Final-Resolution/ChronoVolt/1.Hardware/ChronoVolt_Control_Rev0.3/datasheets/8-MD-06INKM模块/code/代码示例工程/test/source/n76e003/gpio.h

/**
 * @file gpio.h
 * @author mangolu (mangolu81@gmail.com)
 * @brief N76E003 GPIO设置定义
 * @version 1.0.0
 * @date 2019-04-21
 *
 * @copyright Copyright (c) 2019 mangolu All righits reserved
 *
 */
/********************************************************************************************************************************************************************************************************/
/************************* GPIO相关寄存器 *************************/

/************************************************** 1、输入输出数据控制相关寄存器 ***************************************************************************/

/************************* P0 – 端口 0 (可位寻址) *************************/
// -------------------------------------------------------------------------
// |   7    |   6    |   5    |   4    |   3    |   2    |   1    |   0    |
// |--------|--------|--------|--------|--------|--------|--------|--------|
// |  P0.7  |  P0.6  |  P0.5  |  P0.4  |  P0.3  |  P0.2  |  P0.1  |  P0.0  |
// |--------|--------|--------|--------|--------|--------|--------|--------|
// |  R/W   |  R/W   |  R/W   |  R/W   |  R/W   |  R/W   |  R/W   |  R/W   |
// -------------------------------------------------------------------------
// 地址：80H    复位值：1111 1111b
// 
// -------------------------------------------------------------------------
//   Bit  |   Name    |  Description
// -------|-----------|-----------------------------------------------------
//   7:0  |  P0[7:0]  |  端口 0
//        |           |  端口 0 是 8-bit 通用 I/O 端口
// -------------------------------------------------------------------------

/************************* P1 – 端口 1 (可位寻址) *************************/
// -------------------------------------------------------------------------
// |   7    |   6    |   5    |   4    |   3    |   2    |   1    |   0    |
// |--------|--------|--------|--------|--------|--------|--------|--------|
// |  P1.7  |  P1.6  |  P1.5  |  P1.4  |  P1.3  |  P1.2  |  P1.1  |  P1.0  |
// |--------|--------|--------|--------|--------|--------|--------|--------|
// |  R/W   |  R/W   |  R/W   |  R/W   |  R/W   |  R/W   |  R/W   |  R/W   |
// -------------------------------------------------------------------------
// 地址：90H    复位值：1111 1111b
// 
// -------------------------------------------------------------------------
//   Bit  |   Name    |  Description
// -------|-----------|-----------------------------------------------------
//   7:0  |  P1[7:0]  |  端口 1
//        |           |  端口 1 是 8-bit 通用 I/O 端口
// -------------------------------------------------------------------------

/************************* P2 – 端口 2 (可位寻址) *************************/
// -------------------------------------------------------------------------
// |   7    |   6    |   5    |   4    |   3    |   2    |   1    |   0    |
// |--------|--------|--------|--------|--------|--------|--------|--------|
// |   0    |   0    |   0    |   0    |   0    |   0    |   0    |  P2.0  |
// |--------|--------|--------|--------|--------|--------|--------|--------|
// |   R    |   R    |   R    |   R    |   R    |   R    |   R    |   R    |
// -------------------------------------------------------------------------
// 地址：A0H    复位值：0000 000Xb
// 
// -------------------------------------------------------------------------
//   Bit  |   Name    |  Description
// -------|-----------|-----------------------------------------------------
//   7:1  |    0      |  保留位
//        |           |  读取始终为0
// -------|-----------|-----------------------------------------------------
//    0   |   P2.0    |  端口 2 第 0 位
//        |           |  当RPD (CONFIG0.2)=0，P2.0为输入高阻管脚。不配置RPD， 
//        |           |  P2.0读取始终为0 
// -------------------------------------------------------------------------

/************************* P3 – 端口 3 (可位寻址) *************************/
// -------------------------------------------------------------------------
// |   7    |   6    |   5    |   4    |   3    |   2    |   1    |   0    |
// |--------|--------|--------|--------|--------|--------|--------|--------|
// |   0    |   0    |   0    |   0    |   0    |   0    |   0    |  P3.0  |
// |--------|--------|--------|--------|--------|--------|--------|--------|
// |   R    |   R    |   R    |   R    |   R    |   R    |   R    |  R/W   |
// -------------------------------------------------------------------------
// 地址：B0H    复位值：0000 0001b
// 
// -------------------------------------------------------------------------
//   Bit  |   Name    |  Description
// -------|-----------|-----------------------------------------------------
//   7:1  |    0      |  保留位
//        |           |  读取始终为0
// -------|-----------|-----------------------------------------------------
//    0   |   P3.0    |  端口 3 第 0 位
//        |           |  当采用内部振荡器作为系统时钟时，P3.0可用作普通管脚使用。
//        |           |  当采用外部晶振输入方式，P3.0脚用作OSCIN，此时对P3.0写
//        |           |  入数值无效，且P3.0读取值为0
// -------------------------------------------------------------------------

/************************************************** 2、输出模式控制寄存器 ***************************************************************************/

/************************* P0M1 – 端口 0模式选择1 *************************/
// -----------------------------------------------------------------------------------------
// |    7     |    6     |    5     |    4     |    3     |    2     |    1     |    0     |
// |----------|----------|----------|----------|----------|----------|----------|----------|
// |  P0M1.7  |  P0M1.6  |  P0M1.5  |  P0M1.4  |  P0M1.3  |  P0M1.2  |  P0M1.1  |  P0M1.0  |
// |----------|----------|----------|----------|----------|----------|----------|----------|
// |   R/W    |   R/W    |   R/W    |   R/W    |   R/W    |   R/W    |   R/W    |   R/W    |
// -----------------------------------------------------------------------------------------
// 地址：B1H, 页: 0    复位值：1111 1111b
// 
// ---------------------------------------------------------------------------
//   Bit  |   Name      |  Description
// -------|-------------|-----------------------------------------------------
//   7:0  |  P0M1[7:0]  |  端口 0 模式选择1
// ---------------------------------------------------------------------------
//  P0M1 和 P0M2 结合用于决定P0每个引脚的I/O模式

/************************* P0M2 – 端口 0 模式选择 2 *************************/
// -----------------------------------------------------------------------------------------
// |    7     |    6     |    5     |    4     |    3     |    2     |    1     |    0     |
// |----------|----------|----------|----------|----------|----------|----------|----------|
// |  P0M2.7  |  P0M2.7  |  P0M2.7  |  P0M2.7  |  P0M2.7  |  P0M2.7  |  P0M2.7  |  P0M2.7  |
// |----------|----------|----------|----------|----------|----------|----------|----------|
// |   R/W    |   R/W    |   R/W    |   R/W    |   R/W    |   R/W    |   R/W    |   R/W    |
// -----------------------------------------------------------------------------------------
// 地址：B2H, 页: 0    复位值：0000 0000b
// 
// ---------------------------------------------------------------------------
//   Bit  |   Name      |  Description
// -------|-------------|-----------------------------------------------------
//   7:0  |  P0M2[7:0]  |  端口 0 模式选择 2
// ---------------------------------------------------------------------------
// P0M1 和 P0M2 结合用于决定P0每个引脚的I/O模式

/************************* P1M1 – 端口 1 模式选择 1 *************************/
// -----------------------------------------------------------------------------------------
// |    7     |    6     |    5     |    4     |    3     |    2     |    1     |    0     |
// |----------|----------|----------|----------|----------|----------|----------|----------|
// |  P1M1.7  |  P1M1.6  |  P1M1.5  |  P1M1.4  |  P1M1.3  |  P1M1.2  |  P1M1.1  |  P1M1.0  |
// |----------|----------|----------|----------|----------|----------|----------|----------|
// |   R/W    |   R/W    |   R/W    |   R/W    |   R/W    |   R/W    |   R/W    |   R/W    |
// -----------------------------------------------------------------------------------------
// 地址：B3H, 页: 0    复位值：1111 1111b
// 
// ---------------------------------------------------------------------------
//   Bit  |   Name      |  Description
// -------|-------------|-----------------------------------------------------
//   7:0  |  P1M1[7:0]  |  端口 1 模式选择 1
// ---------------------------------------------------------------------------
// P1M1 和 P1M2 结合用于决定P1每个引脚的I/O模式

/************************* P1M2 – 端口 1 模式选择2 *************************/
// -----------------------------------------------------------------------------------------
// |    7     |    6     |    5     |    4     |    3     |    2     |    1     |    0     |
// |----------|----------|----------|----------|----------|----------|----------|----------|
// |  P1M2.7  |  P1M2.6  |  P1M2.5  |  P1M2.4  |  P1M2.3  |  P1M2.2  |  P1M2.1  |  P1M2.0  |
// |----------|----------|----------|----------|----------|----------|----------|----------|
// |   R/W    |   R/W    |   R/W    |   R/W    |   R/W    |   R/W    |   R/W    |   R/W    |
// -----------------------------------------------------------------------------------------
// 地址：B4H, 页: 0    复位值：0000 0000b
// 
// ---------------------------------------------------------------------------
//   Bit  |   Name      |  Description
// -------|-------------|-----------------------------------------------------
//   7:0  |  P1M2[7:0]  |  端口 1 模式选择2
// ---------------------------------------------------------------------------
// P1M1 和 P1M2 结合用于决定P1每个引脚的I/O模式

/************************* P2S – P20 设置及定时器0/1输出使能 *************************/
// ---------------------------------------------------------------------------
// |   7     |   6    |   5    |   4    |   3    |   2    |   1    |   0     |
// |---------|--------|--------|--------|--------|--------|--------|---------|
// |  P20UP  |   -    |   -    |   -    |  T1OE  |  T0OE  |   -    |  P2S.0  |
// |---------|--------|--------|--------|--------|--------|--------|---------|
// |  R/W    |   -    |   -    |   -    |  R/W   |  R/W   |   -    |  R/W    |
// ---------------------------------------------------------------------------
// 地址：B5H    复位值：0000 0000b
// 
// -------------------------------------------------------------------------------------
//   Bit  |   Name    |  Description
// -------|-----------|-----------------------------------------------------------------
//    7   |   P20UP   |  P2.0 上拉使能位
//        |           |  0 = P2.0 禁止上拉
//        |           |  1 = P2.0 使能上拉
//        |           |  仅当RPD (CONFIG0.2)为0时该位有效。如果作为RST#引脚，上拉总是被使能
// -------|-----------|-----------------------------------------------------------------
//    3   |   T1OE    |  定时器 1 输出使能位
//        |           |  0 = 禁止定时器 1 输出
//        |           |  1 = 使能定时器 1 输出从T1引脚
//        |           |  注意：仅当运行在定时器模式时，定时器1输出才会被使能
// -------|-----------|-----------------------------------------------------------------
//    2   |   T0OE    |  定时器 0 输出使能位
//        |           |  0 = 禁止定时器 0  输出
//        |           |  1 = 使能定时器 0  输出从T0引脚
//        |           |  注意：仅当运行在定时器模式时，定时器0输出才会被使能
// -------|-----------|-----------------------------------------------------------------
//    0   |   P2S.0   |  P2.0 施密特触发输入选择
//        |           |  0 = P2.0 TTL电平输入
//        |           |  1 = P2.0 施密特触发输入
// -------------------------------------------------------------------------------------

/************************* P3M1 – 端口 3 模式选择 1 *************************/
// ------------------------------------------------------------------------------
// |   7    |   6    |   5    |   4    |   3    |   2    |   1    |   0         |
// |--------|--------|--------|--------|--------|--------|--------|-------------|
// |   -    |   -    |   -    |   -    |   -    |   -    |   -    |  P3M1.0[3]  |
// |--------|--------|--------|--------|--------|--------|--------|-------------|
// |   -    |   -    |   -    |   -    |   -    |   -    |   -    |    R/W      |
// ------------------------------------------------------------------------------
// 地址：ACH, 页: 0    复位值：0000 0001b
// 
// -------------------------------------------------------------------------
//   Bit  |   Name    |  Description
// -------|-----------|-----------------------------------------------------
//    0   |  P3M1.0   |  端口 3 模式选择 1
// -------------------------------------------------------------------------
// [3] P3M1 和 P3M2结合用于决定P3每个引脚的I/O模式

/************************* P3M2 – 端口3 模式选择 2 *************************/
// ------------------------------------------------------------------------------
// |   7    |   6    |   5    |   4    |   3    |   2    |   1    |     0       |
// |--------|--------|--------|--------|--------|--------|--------|-------------|
// |   -    |   -    |   -    |   -    |   -    |   -    |   -    |  P3M2.0[3]  |
// |--------|--------|--------|--------|--------|--------|--------|-------------|
// |   -    |   -    |   -    |   -    |   -    |   -    |   -    |    R/W      |
// ------------------------------------------------------------------------------
// 地址：ADH, 页: 0    复位值：0000 0000b
// 
// -------------------------------------------------------------------------
//   Bit  |   Name    |  Description
// -------|-----------|-----------------------------------------------------
//    0   |  P3M2.0   |  端口3 模式选择 2
// -------------------------------------------------------------------------
// [3] P3M1 和 P3M2结合用于决定P3每个引脚的I/O模式

/************************************************** 3、输入类型寄存器 ***************************************************************************/

/************************* P0S – 端口 0 施密特触发输入 *************************/
// ---------------------------------------------------------------------------------
// |   7     |   6     |   5     |   4     |   3     |   2     |   1     |   0     |
// |---------|---------|---------|---------|---------|---------|---------|---------|
// |  P0S.7  |  P0S.6  |  P0S.5  |  P0S.4  |  P0S.3  |  P0S.2  |  P0S.1  |  P0S.0  |
// |---------|---------|---------|---------|---------|---------|---------|---------|
// |  R/W    |  R/W    |  R/W    |  R/W    |  R/W    |  R/W    |  R/W    |  R/W    |
// ---------------------------------------------------------------------------------
// 地址：B1H, 页: 1    复位值：0000 0000b
// 
// -------------------------------------------------------------------------
//   Bit  |   Name    |  Description
// -------|-----------|-----------------------------------------------------
//   7:0  |   P0S.n   |  P0.n 施密特触发输入使能位
//        |           |  0 = P0.n TTL 电平输入
//        |           |  1 = P0.n 施密特触发输入
// -------------------------------------------------------------------------

/************************* P1S – 端口 1施密特触发输入 *************************/
// ---------------------------------------------------------------------------------
// |   7     |   6     |   5     |   4     |   3     |   2     |   1     |   0     |
// |---------|---------|---------|---------|---------|---------|---------|---------|
// |  P1S.7  |  P1S.6  |  P1S.5  |  P1S.4  |  P1S.3  |  P1S.2  |  P1S.1  |  P1S.0  |
// |---------|---------|---------|---------|---------|---------|---------|---------|
// |  R/W    |  R/W    |  R/W    |  R/W    |  R/W    |  R/W    |  R/W    |  R/W    |
// ---------------------------------------------------------------------------------
// 地址：B3H, 页: 1    复位值：0000 0000b
// 
// -------------------------------------------------------------------------
//   Bit  |   Name    |  Description
// -------|-----------|-----------------------------------------------------
//   7:0  |   P1S.n   |  P1.n 施密特触发输入选择
//        |           |  0 = P1.n TTL电平输入
//        |           |  1 = P1.n 施密特触发输入
// -------------------------------------------------------------------------

/************************* P2S – P20 设置及定时器0/1输出使能 *************************/
// ---------------------------------------------------------------------------
// |   7     |   6    |   5    |   4    |   3    |   2    |   1    |   0     |
// |---------|--------|--------|--------|--------|--------|--------|---------|
// |  P20UP  |   -    |   -    |   -    |  T1OE  |  T0OE  |   -    |  P2S.0  |
// |---------|--------|--------|--------|--------|--------|--------|---------|
// |  R/W    |   -    |   -    |   -    |  R/W   |  R/W   |   -    |  R/W    |
// ---------------------------------------------------------------------------
// 地址：B5H    复位值：0000 0000b
// 
// -------------------------------------------------------------------------------------
//   Bit  |   Name    |  Description
// -------|-----------|-----------------------------------------------------------------
//    7   |   P20UP   |  P2.0 上拉使能位
//        |           |  0 = P2.0 禁止上拉
//        |           |  1 = P2.0 使能上拉
//        |           |  仅当RPD (CONFIG0.2)为0时该位有效。如果作为RST#引脚，上拉总是被使能
// -------|-----------|-----------------------------------------------------------------
//    3   |   T1OE    |  定时器 1 输出使能位
//        |           |  0 = 禁止定时器 1 输出
//        |           |  1 = 使能定时器 1 输出从T1引脚
//        |           |  注意：仅当运行在定时器模式时，定时器1输出才会被使能
// -------|-----------|-----------------------------------------------------------------
//    2   |   T0OE    |  定时器 0 输出使能位
//        |           |  0 = 禁止定时器 0  输出
//        |           |  1 = 使能定时器 0  输出从T0引脚
//        |           |  注意：仅当运行在定时器模式时，定时器0输出才会被使能
// -------|-----------|-----------------------------------------------------------------
//    0   |   P2S.0   |  P2.0 施密特触发输入选择
//        |           |  0 = P2.0 TTL电平输入
//        |           |  1 = P2.0 施密特触发输入
// -------------------------------------------------------------------------------------

/************************* P3S – 端口 3施密特触发输入 *************************/
// --------------------------------------------------------------------------
// |   7    |   6    |   5    |   4    |   3    |   2    |   1    |   0     |
// |--------|--------|--------|--------|--------|--------|--------|---------|
// |   -    |   -    |   -    |   -    |   -    |   -    |   -    |  P3S.0  |
// |--------|--------|--------|--------|--------|--------|--------|---------|
// |   -    |   -    |   -    |   -    |   -    |   -    |   -    |  R/W    |
// --------------------------------------------------------------------------
// 地址：ACH, 页: 1    复位值：0000 0000b
// 
// -------------------------------------------------------------------------
//   Bit  |   Name    |  Description
// -------|-----------|-----------------------------------------------------
//    0   |  P3S.0    |  P3.0 施密特触发输入选择
//        |           |  0 = P3.0 TTL电平输入
//        |           |  1 = P3.0 施密特触发输入
// -------------------------------------------------------------------------

/************************************************** 4、输出斜率控制寄存器 ***************************************************************************/

/************************* P0SR – 端口 0 斜率控制 *************************/
// -----------------------------------------------------------------------------------------
// |    7     |    6     |    5     |    4     |    3     |    2     |    1     |    0     |
// |----------|----------|----------|----------|----------|----------|----------|----------|
// |  P0SR.7  |  P0SR.6  |  P0SR.5  |  P0SR.4  |  P0SR.3  |  P0SR.2  |  P0SR.1  |  P0SR.0  |
// |----------|----------|----------|----------|----------|----------|----------|----------|
// |   R/W    |   R/W    |   R/W    |   R/W    |   R/W    |   R/W    |   R/W    |   R/W    |
// -----------------------------------------------------------------------------------------
// 地址：B2H, 页: 1    复位值：0000 0000b
// 
// -------------------------------------------------------------------------
//   Bit  |   Name    |  Description
// -------|-----------|-----------------------------------------------------
//   7:0  |  P0SR.n   |  P0.n 斜率控制
//        |           |  0 = P0.n 普通输出
//        |           |  1 = P0.n 高速输出
// -------------------------------------------------------------------------

/************************* P1SR – 端口 1 斜率控制 *************************/
// -----------------------------------------------------------------------------------------
// |    7     |    6     |    5     |    4     |    3     |    2     |    1     |    0     |
// |----------|----------|----------|----------|----------|----------|----------|----------|
// |  P1SR.7  |  P1SR.6  |  P1SR.5  |  P1SR.4  |  P1SR.3  |  P1SR.2  |  P1SR.1  |  P1SR.0  |
// |----------|----------|----------|----------|----------|----------|----------|----------|
// |   R/W    |   R/W    |   R/W    |   R/W    |   R/W    |   R/W    |   R/W    |   R/W    |
// -----------------------------------------------------------------------------------------
// 地址：B4H, 页: 1    复位值：0000 0000b
// 
// -------------------------------------------------------------------------
//   Bit  |   Name    |  Description
// -------|-----------|-----------------------------------------------------
//   7:0  |  P1SR.n   |  P1.n 斜率控制
//        |           |  0 = P1.n 普通输出
//        |           |  1 = P1.n 高速输出
// -------------------------------------------------------------------------

/************************* P3SR – 端口 3 斜率控制 *************************/
// ---------------------------------------------------------------------------
// |   7    |   6    |   5    |   4    |   3    |   2    |   1    |    0     |
// |--------|--------|--------|--------|--------|--------|--------|----------|
// |   -    |   -    |   -    |   -    |   -    |   -    |   -    |  P3SR.0  |
// |--------|--------|--------|--------|--------|--------|--------|----------|
// |   -    |   -    |   -    |   -    |   -    |   -    |   -    |   R/W    |
// ---------------------------------------------------------------------------
// 地址：ADH, 页: 1    复位值：0000 0000b
// 
// -------------------------------------------------------------------------
//   Bit  |   Name    |  Description
// -------|-----------|-----------------------------------------------------
//    0   |  P3SR.0   |  P3.n 斜率控制
//        |           |  0 = P3.0 普通输出
//        |           |  1 = P3.0 高速输出
// -------------------------------------------------------------------------

/********************************************************************************************************************************************************************************************************/
#ifndef _GPIO_H_
#define _GPIO_H_

/** 所需头文件开始>>> */

#include "N76E003.h"
#include "../common/common.h"

/** 所需头文件结束<<< */

/** 需要自行定义部分开始>>> */

extern bit BIT_TMP;	/** 比特位存储临时变量，定义于common.c文件中 */

/** 需要自行定义部分结束<<< */

/********************************************************************************************************************************************************************************************************/
/************************* 设置端口为准双向模式(Quasi Mode)（标准8051端口结构） *************************/
#define SET_P00_Quasi_Mode		P0M1&=~SET_BIT0;P0M2&=~SET_BIT0		/** 设置P0^0为准双向模式 */
#define SET_P01_Quasi_Mode		P0M1&=~SET_BIT1;P0M2&=~SET_BIT1		/** 设置P0^1为准双向模式 */
#define SET_P02_Quasi_Mode		P0M1&=~SET_BIT2;P0M2&=~SET_BIT2		/** 设置P0^2为准双向模式 */
#define SET_P03_Quasi_Mode		P0M1&=~SET_BIT3;P0M2&=~SET_BIT3		/** 设置P0^3为准双向模式 */
#define SET_P04_Quasi_Mode		P0M1&=~SET_BIT4;P0M2&=~SET_BIT4		/** 设置P0^4为准双向模式 */
#define SET_P05_Quasi_Mode		P0M1&=~SET_BIT5;P0M2&=~SET_BIT5		/** 设置P0^5为准双向模式 */
#define SET_P06_Quasi_Mode		P0M1&=~SET_BIT6;P0M2&=~SET_BIT6		/** 设置P0^6为准双向模式 */
#define SET_P07_Quasi_Mode		P0M1&=~SET_BIT7;P0M2&=~SET_BIT7		/** 设置P0^7为准双向模式 */
#define SET_P10_Quasi_Mode		P1M1&=~SET_BIT0;P1M2&=~SET_BIT0		/** 设置P1^0为准双向模式 */
#define SET_P11_Quasi_Mode		P1M1&=~SET_BIT1;P1M2&=~SET_BIT1		/** 设置P1^1为准双向模式 */
#define SET_P12_Quasi_Mode		P1M1&=~SET_BIT2;P1M2&=~SET_BIT2		/** 设置P1^2为准双向模式 */
#define SET_P13_Quasi_Mode		P1M1&=~SET_BIT3;P1M2&=~SET_BIT3		/** 设置P1^3为准双向模式 */
#define SET_P14_Quasi_Mode		P1M1&=~SET_BIT4;P1M2&=~SET_BIT4		/** 设置P1^4为准双向模式 */
#define SET_P15_Quasi_Mode		P1M1&=~SET_BIT5;P1M2&=~SET_BIT5		/** 设置P1^5为准双向模式 */
#define SET_P16_Quasi_Mode		P1M1&=~SET_BIT6;P1M2&=~SET_BIT6		/** 设置P1^6为准双向模式 */
#define SET_P17_Quasi_Mode		P1M1&=~SET_BIT7;P1M2&=~SET_BIT7		/** 设置P1^7为准双向模式 */
#define SET_P30_Quasi_Mode		P3M1&=~SET_BIT0;P3M2&=~SET_BIT0		/** 设置P3^0为准双向模式 */
#define SET_P0_Quasi_Mode		P0M1=0x00;P0M2=0x00					/** 设置P0端口为准双向模式 */
#define SET_P1_Quasi_Mode		P1M1=0x00;P1M2=0x00					/** 设置P1端口为准双向模式 */

/********************************************************************************************************************************************************************************************************/

/********************************************************************************************************************************************************************************************************/
/************************* 设置端口为推挽输出模式(Push Pull Mode) *************************/
#define SET_P00_PushPull_Mode		P0M1&=~SET_BIT0;P0M2|=SET_BIT0		/** 设置P0^0为推挽输出模式 */
#define SET_P01_PushPull_Mode		P0M1&=~SET_BIT1;P0M2|=SET_BIT1		/** 设置P0^1为推挽输出模式 */
#define SET_P02_PushPull_Mode		P0M1&=~SET_BIT2;P0M2|=SET_BIT2		/** 设置P0^2为推挽输出模式 */
#define SET_P03_PushPull_Mode		P0M1&=~SET_BIT3;P0M2|=SET_BIT3		/** 设置P0^3为推挽输出模式 */
#define SET_P04_PushPull_Mode		P0M1&=~SET_BIT4;P0M2|=SET_BIT4		/** 设置P0^4为推挽输出模式 */
#define SET_P05_PushPull_Mode		P0M1&=~SET_BIT5;P0M2|=SET_BIT5		/** 设置P0^5为推挽输出模式 */
#define SET_P06_PushPull_Mode		P0M1&=~SET_BIT6;P0M2|=SET_BIT6		/** 设置P0^6为推挽输出模式 */
#define SET_P07_PushPull_Mode		P0M1&=~SET_BIT7;P0M2|=SET_BIT7		/** 设置P0^7为推挽输出模式 */
#define SET_P10_PushPull_Mode		P1M1&=~SET_BIT0;P1M2|=SET_BIT0		/** 设置P1^0为推挽输出模式 */
#define SET_P11_PushPull_Mode		P1M1&=~SET_BIT1;P1M2|=SET_BIT1		/** 设置P1^1为推挽输出模式 */
#define SET_P12_PushPull_Mode		P1M1&=~SET_BIT2;P1M2|=SET_BIT2		/** 设置P1^2为推挽输出模式 */
#define SET_P13_PushPull_Mode		P1M1&=~SET_BIT3;P1M2|=SET_BIT3		/** 设置P1^3为推挽输出模式 */
#define SET_P14_PushPull_Mode		P1M1&=~SET_BIT4;P1M2|=SET_BIT4		/** 设置P1^4为推挽输出模式 */
#define SET_P15_PushPull_Mode		P1M1&=~SET_BIT5;P1M2|=SET_BIT5		/** 设置P1^5为推挽输出模式 */
#define SET_P16_PushPull_Mode		P1M1&=~SET_BIT6;P1M2|=SET_BIT6		/** 设置P1^6为推挽输出模式 */
#define SET_P17_PushPull_Mode		P1M1&=~SET_BIT7;P1M2|=SET_BIT7		/** 设置P1^7为推挽输出模式 */
#define SET_P30_PushPull_Mode		P3M1&=~SET_BIT0;P3M2|=SET_BIT0		/** 设置P3^0为推挽输出模式 */
#define SET_P0_PushPull_Mode		P0M1=0x00;P0M2=0xFF					/** 设置P0端口为推挽输出模式 */
#define SET_P1_PushPull_Mode		P1M1=0x00;P1M2=0xFF					/** 设置P1端口为推挽输出模式 */

/********************************************************************************************************************************************************************************************************/

/********************************************************************************************************************************************************************************************************/
/************************* 设置端口为输入模式(高阻)(Input Only Mode) *************************/
#define SET_P00_Input_Mode		P0M1|=SET_BIT0;P0M2&=~SET_BIT0		/** 设置P0^0为输入模式 */
#define SET_P01_Input_Mode		P0M1|=SET_BIT1;P0M2&=~SET_BIT1		/** 设置P0^1为输入模式 */
#define SET_P02_Input_Mode		P0M1|=SET_BIT2;P0M2&=~SET_BIT2		/** 设置P0^2为输入模式 */
#define SET_P03_Input_Mode		P0M1|=SET_BIT3;P0M2&=~SET_BIT3		/** 设置P0^3为输入模式 */
#define SET_P04_Input_Mode		P0M1|=SET_BIT4;P0M2&=~SET_BIT4		/** 设置P0^4为输入模式 */
#define SET_P05_Input_Mode		P0M1|=SET_BIT5;P0M2&=~SET_BIT5		/** 设置P0^5为输入模式 */
#define SET_P06_Input_Mode		P0M1|=SET_BIT6;P0M2&=~SET_BIT6		/** 设置P0^6为输入模式 */
#define SET_P07_Input_Mode		P0M1|=SET_BIT7;P0M2&=~SET_BIT7		/** 设置P0^7为输入模式 */
#define SET_P10_Input_Mode		P1M1|=SET_BIT0;P1M2&=~SET_BIT0		/** 设置P1^0为输入模式 */
#define SET_P11_Input_Mode		P1M1|=SET_BIT1;P1M2&=~SET_BIT1		/** 设置P1^1为输入模式 */
#define SET_P12_Input_Mode		P1M1|=SET_BIT2;P1M2&=~SET_BIT2		/** 设置P1^2为输入模式 */
#define SET_P13_Input_Mode		P1M1|=SET_BIT3;P1M2&=~SET_BIT3		/** 设置P1^3为输入模式 */
#define SET_P14_Input_Mode		P1M1|=SET_BIT4;P1M2&=~SET_BIT4		/** 设置P1^4为输入模式 */
#define SET_P15_Input_Mode		P1M1|=SET_BIT5;P1M2&=~SET_BIT5		/** 设置P1^5为输入模式 */
#define SET_P16_Input_Mode		P1M1|=SET_BIT6;P1M2&=~SET_BIT6		/** 设置P1^6为输入模式 */
#define SET_P17_Input_Mode		P1M1|=SET_BIT7;P1M2&=~SET_BIT7		/** 设置P1^7为输入模式 */
#define SET_P30_Input_Mode		P3M1|=SET_BIT0;P3M2&=~SET_BIT0		/** 设置P3^0为输入模式 */
#define SET_P0_Input_Mode		P0M1=0xFF;P0M2=0x00					/** 设置P0端口为输入模式 */
#define SET_P1_Input_Mode		P1M1=0xFF;P1M2=0x00					/** 设置P1端口为输入模式 */

/********************************************************************************************************************************************************************************************************/

/********************************************************************************************************************************************************************************************************/
/************************* 设置端口为开漏模式(Open Drain Mode) *************************/
#define SET_P00_OpenDrain_Mode		P0M1|=SET_BIT0;P0M2|=SET_BIT0		/** 设置P0^0为开漏模式 */
#define SET_P01_OpenDrain_Mode		P0M1|=SET_BIT1;P0M2|=SET_BIT1		/** 设置P0^1为开漏模式 */
#define SET_P02_OpenDrain_Mode		P0M1|=SET_BIT2;P0M2|=SET_BIT2		/** 设置P0^2为开漏模式 */
#define SET_P03_OpenDrain_Mode		P0M1|=SET_BIT3;P0M2|=SET_BIT3		/** 设置P0^3为开漏模式 */
#define SET_P04_OpenDrain_Mode		P0M1|=SET_BIT4;P0M2|=SET_BIT4		/** 设置P0^4为开漏模式 */
#define SET_P05_OpenDrain_Mode		P0M1|=SET_BIT5;P0M2|=SET_BIT5		/** 设置P0^5为开漏模式 */
#define SET_P06_OpenDrain_Mode		P0M1|=SET_BIT6;P0M2|=SET_BIT6		/** 设置P0^6为开漏模式 */
#define SET_P07_OpenDrain_Mode		P0M1|=SET_BIT7;P0M2|=SET_BIT7		/** 设置P0^7为开漏模式 */
#define SET_P10_OpenDrain_Mode		P1M1|=SET_BIT0;P1M2|=SET_BIT0		/** 设置P1^0为开漏模式 */
#define SET_P11_OpenDrain_Mode		P1M1|=SET_BIT1;P1M2|=SET_BIT1		/** 设置P1^1为开漏模式 */
#define SET_P12_OpenDrain_Mode		P1M1|=SET_BIT2;P1M2|=SET_BIT2		/** 设置P1^2为开漏模式 */
#define SET_P13_OpenDrain_Mode		P1M1|=SET_BIT3;P1M2|=SET_BIT3		/** 设置P1^3为开漏模式 */
#define SET_P14_OpenDrain_Mode		P1M1|=SET_BIT4;P1M2|=SET_BIT4		/** 设置P1^4为开漏模式 */
#define SET_P15_OpenDrain_Mode		P1M1|=SET_BIT5;P1M2|=SET_BIT5		/** 设置P1^5为开漏模式 */
#define SET_P16_OpenDrain_Mode		P1M1|=SET_BIT6;P1M2|=SET_BIT6		/** 设置P1^6为开漏模式 */
#define SET_P17_OpenDrain_Mode		P1M1|=SET_BIT7;P1M2|=SET_BIT7		/** 设置P1^7为开漏模式 */
#define SET_P30_OpenDrain_Mode		P3M1|=SET_BIT0;P3M2|=SET_BIT0		/** 设置P3^0为开漏模式 */
#define SET_P0_OpenDrain_Mode		P0M1=0xFF;P0M2=0xFF					/** 设置P0端口为开漏模式 */
#define SET_P1_OpenDrain_Mode		P1M1=0xFF;P1M2=0xFF					/** 设置P1端口为开漏模式 */

/********************************************************************************************************************************************************************************************************/

/********************************************************************************************************************************************************************************************************/
/************************* 设置P0端口输入类型(默认为TTL输入类型) *************************/
#define SET_P00_TTL_INPUT_TYPE			BIT_TMP=EA;EA=0;TA=0xAA;TA=0x55;SFRS=0x01;P0S&=~SET_BIT0;TA=0xAA;TA=0x55;SFRS=0x00;EA=BIT_TMP		/** 设置P0^0为TTL输入类型 */
#define SET_P01_TTL_INPUT_TYPE			BIT_TMP=EA;EA=0;TA=0xAA;TA=0x55;SFRS=0x01;P0S&=~SET_BIT1;TA=0xAA;TA=0x55;SFRS=0x00;EA=BIT_TMP		/** 设置P0^1为TTL输入类型 */
#define SET_P02_TTL_INPUT_TYPE			BIT_TMP=EA;EA=0;TA=0xAA;TA=0x55;SFRS=0x01;P0S&=~SET_BIT2;TA=0xAA;TA=0x55;SFRS=0x00;EA=BIT_TMP		/** 设置P0^2为TTL输入类型 */
#define SET_P03_TTL_INPUT_TYPE			BIT_TMP=EA;EA=0;TA=0xAA;TA=0x55;SFRS=0x01;P0S&=~SET_BIT3;TA=0xAA;TA=0x55;SFRS=0x00;EA=BIT_TMP		/** 设置P0^3为TTL输入类型 */
#define SET_P04_TTL_INPUT_TYPE			BIT_TMP=EA;EA=0;TA=0xAA;TA=0x55;SFRS=0x01;P0S&=~SET_BIT4;TA=0xAA;TA=0x55;SFRS=0x00;EA=BIT_TMP		/** 设置P0^4为TTL输入类型 */
#define SET_P05_TTL_INPUT_TYPE			BIT_TMP=EA;EA=0;TA=0xAA;TA=0x55;SFRS=0x01;P0S&=~SET_BIT5;TA=0xAA;TA=0x55;SFRS=0x00;EA=BIT_TMP		/** 设置P0^5为TTL输入类型 */
#define SET_P06_TTL_INPUT_TYPE			BIT_TMP=EA;EA=0;TA=0xAA;TA=0x55;SFRS=0x01;P0S&=~SET_BIT6;TA=0xAA;TA=0x55;SFRS=0x00;EA=BIT_TMP		/** 设置P0^6为TTL输入类型 */
#define SET_P07_TTL_INPUT_TYPE			BIT_TMP=EA;EA=0;TA=0xAA;TA=0x55;SFRS=0x01;P0S&=~SET_BIT7;TA=0xAA;TA=0x55;SFRS=0x00;EA=BIT_TMP		/** 设置P0^7为TTL输入类型 */

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

/********************************************************************************************************************************************************************************************************/

/********************************************************************************************************************************************************************************************************/
/************************* 设置P2端口输入类型(默认为TTL输入类型)(P2^0只能做为输入，不能做输出) *************************/
#define SET_P20_TTL_INPUT_TYPE			BIT_TMP=EA;EA=0;TA=0xAA;TA=0x55;SFRS=0x01;P2S&=~SET_BIT0;TA=0xAA;TA=0x55;SFRS=0x00;EA=BIT_TMP		/** 设置P2^0为TTL输入类型 */

/************************* 设置P2端口输入类型(默认为史密斯触发输入类型)(P2^0只能做为输入，不能做输出) *************************/
#define SET_P20_SCHMITT_INPUT_TYPE		BIT_TMP=EA;EA=0;TA=0xAA;TA=0x55;SFRS=0x01;P2S|=SET_BIT0;TA=0xAA;TA=0x55;SFRS=0x00;EA=BIT_TMP		/** 设置P2^0为史密斯触发输入类型 */

/********************************************************************************************************************************************************************************************************/

/********************************************************************************************************************************************************************************************************/

/************************* 设置P3端口输入类型(默认为TTL输入类型)(P2^0只能做为输入，不能做输出) *************************/
#define SET_P30_TTL_INPUT_TYPE			BIT_TMP=EA;EA=0;TA=0xAA;TA=0x55;SFRS=0x01;P3S&=~SET_BIT0;TA=0xAA;TA=0x55;SFRS=0x00;EA=BIT_TMP		/** 设置P3^0为TTL输入类型 */

/************************* 设置P3端口输入类型(默认为史密斯触发输入类型)(P2^0只能做为输入，不能做输出) *************************/
#define SET_P30_SCHMITT_INPUT_TYPE		BIT_TMP=EA;EA=0;TA=0xAA;TA=0x55;SFRS=0x01;P3S|=SET_BIT0;TA=0xAA;TA=0x55;SFRS=0x00;EA=BIT_TMP		/** 设置P3^0为史密斯触发输入类型 */

/********************************************************************************************************************************************************************************************************/

/********************************************************************************************************************************************************************************************************/

/************************* 设置P0端口输出斜率为普通输出(默认为普通输出) *************************/
#define SET_P00_OUTPUT_SLEW_RATE_NORMAL_SPEED		BIT_TMP=EA;EA=0;TA=0xAA;TA=0x55;SFRS=0x01;P0SR&=~SET_BIT0;TA=0xAA;TA=0x55;SFRS=0x00;EA=BIT_TMP	/** 设置端口P0^0输出斜率为普通输出 */
#define SET_P01_OUTPUT_SLEW_RATE_NORMAL_SPEED		BIT_TMP=EA;EA=0;TA=0xAA;TA=0x55;SFRS=0x01;P0SR&=~SET_BIT1;TA=0xAA;TA=0x55;SFRS=0x00;EA=BIT_TMP	/** 设置端口P0^1输出斜率为普通输出 */
#define SET_P02_OUTPUT_SLEW_RATE_NORMAL_SPEED		BIT_TMP=EA;EA=0;TA=0xAA;TA=0x55;SFRS=0x01;P0SR&=~SET_BIT2;TA=0xAA;TA=0x55;SFRS=0x00;EA=BIT_TMP	/** 设置端口P0^2输出斜率为普通输出 */
#define SET_P03_OUTPUT_SLEW_RATE_NORMAL_SPEED		BIT_TMP=EA;EA=0;TA=0xAA;TA=0x55;SFRS=0x01;P0SR&=~SET_BIT3;TA=0xAA;TA=0x55;SFRS=0x00;EA=BIT_TMP	/** 设置端口P0^3输出斜率为普通输出 */
#define SET_P04_OUTPUT_SLEW_RATE_NORMAL_SPEED		BIT_TMP=EA;EA=0;TA=0xAA;TA=0x55;SFRS=0x01;P0SR&=~SET_BIT4;TA=0xAA;TA=0x55;SFRS=0x00;EA=BIT_TMP	/** 设置端口P0^4输出斜率为普通输出 */
#define SET_P05_OUTPUT_SLEW_RATE_NORMAL_SPEED		BIT_TMP=EA;EA=0;TA=0xAA;TA=0x55;SFRS=0x01;P0SR&=~SET_BIT5;TA=0xAA;TA=0x55;SFRS=0x00;EA=BIT_TMP	/** 设置端口P0^5输出斜率为普通输出 */
#define SET_P06_OUTPUT_SLEW_RATE_NORMAL_SPEED		BIT_TMP=EA;EA=0;TA=0xAA;TA=0x55;SFRS=0x01;P0SR&=~SET_BIT6;TA=0xAA;TA=0x55;SFRS=0x00;EA=BIT_TMP	/** 设置端口P0^6输出斜率为普通输出 */
#define SET_P07_OUTPUT_SLEW_RATE_NORMAL_SPEED		BIT_TMP=EA;EA=0;TA=0xAA;TA=0x55;SFRS=0x01;P0SR&=~SET_BIT7;TA=0xAA;TA=0x55;SFRS=0x00;EA=BIT_TMP	/** 设置端口P0^7输出斜率为普通输出 */
#define SET_P0_OUTPUT_SLEW_RATE_NORMAL_SPEED		BIT_TMP=EA;EA=0;TA=0xAA;TA=0x55;SFRS=0x01;P0SR=0x00;TA=0xAA;TA=0x55;SFRS=0x00;EA=BIT_TMP		/** 设置端口P0输出斜率为普通输出 */

/************************* 设置P0端口输出斜率为高速输出(默认为普通输出) *************************/
#define SET_P00_OUTPUT_SLEW_RATE_HIGH_SPEED			BIT_TMP=EA;EA=0;TA=0xAA;TA=0x55;SFRS=0x01;P0SR|=SET_BIT0;TA=0xAA;TA=0x55;SFRS=0x00;EA=BIT_TMP	/** 设置端口P0^0输出斜率为高速输出 */
#define SET_P01_OUTPUT_SLEW_RATE_HIGH_SPEED			BIT_TMP=EA;EA=0;TA=0xAA;TA=0x55;SFRS=0x01;P0SR|=SET_BIT1;TA=0xAA;TA=0x55;SFRS=0x00;EA=BIT_TMP	/** 设置端口P0^1输出斜率为高速输出 */
#define SET_P02_OUTPUT_SLEW_RATE_HIGH_SPEED			BIT_TMP=EA;EA=0;TA=0xAA;TA=0x55;SFRS=0x01;P0SR|=SET_BIT2;TA=0xAA;TA=0x55;SFRS=0x00;EA=BIT_TMP	/** 设置端口P0^2输出斜率为高速输出 */
#define SET_P03_OUTPUT_SLEW_RATE_HIGH_SPEED			BIT_TMP=EA;EA=0;TA=0xAA;TA=0x55;SFRS=0x01;P0SR|=SET_BIT3;TA=0xAA;TA=0x55;SFRS=0x00;EA=BIT_TMP	/** 设置端口P0^3输出斜率为高速输出 */
#define SET_P04_OUTPUT_SLEW_RATE_HIGH_SPEED			BIT_TMP=EA;EA=0;TA=0xAA;TA=0x55;SFRS=0x01;P0SR|=SET_BIT4;TA=0xAA;TA=0x55;SFRS=0x00;EA=BIT_TMP	/** 设置端口P0^4输出斜率为高速输出 */
#define SET_P05_OUTPUT_SLEW_RATE_HIGH_SPEED			BIT_TMP=EA;EA=0;TA=0xAA;TA=0x55;SFRS=0x01;P0SR|=SET_BIT5;TA=0xAA;TA=0x55;SFRS=0x00;EA=BIT_TMP	/** 设置端口P0^5输出斜率为高速输出 */
#define SET_P06_OUTPUT_SLEW_RATE_HIGH_SPEED			BIT_TMP=EA;EA=0;TA=0xAA;TA=0x55;SFRS=0x01;P0SR|=SET_BIT6;TA=0xAA;TA=0x55;SFRS=0x00;EA=BIT_TMP	/** 设置端口P0^6输出斜率为高速输出 */
#define SET_P07_OUTPUT_SLEW_RATE_HIGH_SPEED			BIT_TMP=EA;EA=0;TA=0xAA;TA=0x55;SFRS=0x01;P0SR|=SET_BIT7;TA=0xAA;TA=0x55;SFRS=0x00;EA=BIT_TMP	/** 设置端口P0^7输出斜率为高速输出 */
#define SET_P0_OUTPUT_SLEW_RATE_HIGH_SPEED			BIT_TMP=EA;EA=0;TA=0xAA;TA=0x55;SFRS=0x01;P0SR=0xFF;TA=0xAA;TA=0x55;SFRS=0x00;EA=BIT_TMP		/** 设置端口P0输出斜率为高速输出 */

/********************************************************************************************************************************************************************************************************/

/********************************************************************************************************************************************************************************************************/
/************************* 设置P1端口输出斜率为普通输出(默认为普通输出) *************************/
#define SET_P10_OUTPUT_SLEW_RATE_NORMAL_SPEED		BIT_TMP=EA;EA=0;TA=0xAA;TA=0x55;SFRS=0x01;P1SR&=~SET_BIT0;TA=0xAA;TA=0x55;SFRS=0x00;EA=BIT_TMP	/** 设置端口P1^0输出斜率为普通输出 */
#define SET_P11_OUTPUT_SLEW_RATE_NORMAL_SPEED		BIT_TMP=EA;EA=0;TA=0xAA;TA=0x55;SFRS=0x01;P1SR&=~SET_BIT1;TA=0xAA;TA=0x55;SFRS=0x00;EA=BIT_TMP	/** 设置端口P1^1输出斜率为普通输出 */
#define SET_P12_OUTPUT_SLEW_RATE_NORMAL_SPEED		BIT_TMP=EA;EA=0;TA=0xAA;TA=0x55;SFRS=0x01;P1SR&=~SET_BIT2;TA=0xAA;TA=0x55;SFRS=0x00;EA=BIT_TMP	/** 设置端口P1^2输出斜率为普通输出 */
#define SET_P13_OUTPUT_SLEW_RATE_NORMAL_SPEED		BIT_TMP=EA;EA=0;TA=0xAA;TA=0x55;SFRS=0x01;P1SR&=~SET_BIT3;TA=0xAA;TA=0x55;SFRS=0x00;EA=BIT_TMP	/** 设置端口P1^3输出斜率为普通输出 */
#define SET_P14_OUTPUT_SLEW_RATE_NORMAL_SPEED		BIT_TMP=EA;EA=0;TA=0xAA;TA=0x55;SFRS=0x01;P1SR&=~SET_BIT4;TA=0xAA;TA=0x55;SFRS=0x00;EA=BIT_TMP	/** 设置端口P1^4输出斜率为普通输出 */
#define SET_P15_OUTPUT_SLEW_RATE_NORMAL_SPEED		BIT_TMP=EA;EA=0;TA=0xAA;TA=0x55;SFRS=0x01;P1SR&=~SET_BIT5;TA=0xAA;TA=0x55;SFRS=0x00;EA=BIT_TMP	/** 设置端口P1^5输出斜率为普通输出 */
#define SET_P16_OUTPUT_SLEW_RATE_NORMAL_SPEED		BIT_TMP=EA;EA=0;TA=0xAA;TA=0x55;SFRS=0x01;P1SR&=~SET_BIT6;TA=0xAA;TA=0x55;SFRS=0x00;EA=BIT_TMP	/** 设置端口P1^6输出斜率为普通输出 */
#define SET_P17_OUTPUT_SLEW_RATE_NORMAL_SPEED		BIT_TMP=EA;EA=0;TA=0xAA;TA=0x55;SFRS=0x01;P1SR&=~SET_BIT7;TA=0xAA;TA=0x55;SFRS=0x00;EA=BIT_TMP	/** 设置端口P1^7输出斜率为普通输出 */
#define SET_P1_OUTPUT_SLEW_RATE_NORMAL_SPEED		BIT_TMP=EA;EA=0;TA=0xAA;TA=0x55;SFRS=0x01;P1SR=0x00;TA=0xAA;TA=0x55;SFRS=0x00;EA=BIT_TMP		/** 设置端口P1输出斜率为普通输出 */

/************************* 设置P1端口输出斜率为高速输出(默认为普通输出) *************************/
#define SET_P10_OUTPUT_SLEW_RATE_HIGH_SPEED			BIT_TMP=EA;EA=0;TA=0xAA;TA=0x55;SFRS=0x01;P1SR|=SET_BIT0;TA=0xAA;TA=0x55;SFRS=0x00;EA=BIT_TMP	/** 设置端口P1^0输出斜率为高速输出 */
#define SET_P11_OUTPUT_SLEW_RATE_HIGH_SPEED			BIT_TMP=EA;EA=0;TA=0xAA;TA=0x55;SFRS=0x01;P1SR|=SET_BIT1;TA=0xAA;TA=0x55;SFRS=0x00;EA=BIT_TMP	/** 设置端口P1^1输出斜率为高速输出 */
#define SET_P12_OUTPUT_SLEW_RATE_HIGH_SPEED			BIT_TMP=EA;EA=0;TA=0xAA;TA=0x55;SFRS=0x01;P1SR|=SET_BIT2;TA=0xAA;TA=0x55;SFRS=0x00;EA=BIT_TMP	/** 设置端口P1^2输出斜率为高速输出 */
#define SET_P13_OUTPUT_SLEW_RATE_HIGH_SPEED			BIT_TMP=EA;EA=0;TA=0xAA;TA=0x55;SFRS=0x01;P1SR|=SET_BIT3;TA=0xAA;TA=0x55;SFRS=0x00;EA=BIT_TMP	/** 设置端口P1^3输出斜率为高速输出 */
#define SET_P14_OUTPUT_SLEW_RATE_HIGH_SPEED			BIT_TMP=EA;EA=0;TA=0xAA;TA=0x55;SFRS=0x01;P1SR|=SET_BIT4;TA=0xAA;TA=0x55;SFRS=0x00;EA=BIT_TMP	/** 设置端口P1^4输出斜率为高速输出 */
#define SET_P15_OUTPUT_SLEW_RATE_HIGH_SPEED			BIT_TMP=EA;EA=0;TA=0xAA;TA=0x55;SFRS=0x01;P1SR|=SET_BIT5;TA=0xAA;TA=0x55;SFRS=0x00;EA=BIT_TMP	/** 设置端口P1^5输出斜率为高速输出 */
#define SET_P16_OUTPUT_SLEW_RATE_HIGH_SPEED			BIT_TMP=EA;EA=0;TA=0xAA;TA=0x55;SFRS=0x01;P1SR|=SET_BIT6;TA=0xAA;TA=0x55;SFRS=0x00;EA=BIT_TMP	/** 设置端口P1^6输出斜率为高速输出 */
#define SET_P17_OUTPUT_SLEW_RATE_HIGH_SPEED			BIT_TMP=EA;EA=0;TA=0xAA;TA=0x55;SFRS=0x01;P1SR|=SET_BIT7;TA=0xAA;TA=0x55;SFRS=0x00;EA=BIT_TMP	/** 设置端口P1^7输出斜率为高速输出 */
#define SET_P1_OUTPUT_SLEW_RATE_HIGH_SPEED			BIT_TMP=EA;EA=0;TA=0xAA;TA=0x55;SFRS=0x01;P1SR=0xFF;TA=0xAA;TA=0x55;SFRS=0x00;EA=BIT_TMP		/** 设置端口P1输出斜率为高速输出 */

/********************************************************************************************************************************************************************************************************/

/********************************************************************************************************************************************************************************************************/
/************************* 设置P3端口输出斜率为普通输出(默认为普通输出) *************************/
#define SET_P30_OUTPUT_SLEW_RATE_NORMAL_SPEED		BIT_TMP=EA;EA=0;TA=0xAA;TA=0x55;SFRS=0x01;P3SR&=~SET_BIT0;TA=0xAA;TA=0x55;SFRS=0x00;EA=BIT_TMP	/** 设置端口P3^0输出斜率为普通输出 */

/************************* 设置P3端口输出斜率为高速输出(默认为普通输出) *************************/
#define SET_P30_OUTPUT_SLEW_RATE_HIGH_SPEED			BIT_TMP=EA;EA=0;TA=0xAA;TA=0x55;SFRS=0x01;P3SR|=SET_BIT0;TA=0xAA;TA=0x55;SFRS=0x00;EA=BIT_TMP	/** 设置端口P3^0输出斜率为高速输出 */

/********************************************************************************************************************************************************************************************************/

/********************************************************************************************************************************************************************************************************/
/************************* 设置P0端口输出 *************************/
#define set_P00		P00 = 1		/** 设置P0^0输出1 */
#define set_P01		P01 = 1		/** 设置P0^1输出1 */
#define set_P02		P02 = 1		/** 设置P0^2输出1 */
#define set_P03		P03 = 1		/** 设置P0^3输出1 */
#define set_P04		P04 = 1		/** 设置P0^4输出1 */
#define set_P05		P05 = 1		/** 设置P0^5输出1 */
#define set_P06		P06 = 1		/** 设置P0^6输出1 */
#define set_P07		P07 = 1		/** 设置P0^7输出1 */

#define clr_P00		P00 = 0		/** 设置P0^0输出0 */
#define clr_P01		P01 = 0		/** 设置P0^1输出0 */
#define clr_P02		P02 = 0		/** 设置P0^2输出0 */
#define clr_P03		P03 = 0		/** 设置P0^3输出0 */
#define clr_P04		P04 = 0		/** 设置P0^4输出0 */
#define clr_P05		P05 = 0		/** 设置P0^5输出0 */
#define clr_P06		P06 = 0		/** 设置P0^6输出0 */
#define clr_P07		P07 = 0		/** 设置P0^7输出0 */

/********************************************************************************************************************************************************************************************************/

/********************************************************************************************************************************************************************************************************/
/************************* 设置P1端口输出 *************************/
#define set_P10		P10 = 1		/** 设置P1^0输出1 */
#define set_P11		P11 = 1		/** 设置P1^1输出1 */
#define set_P12		P12 = 1		/** 设置P1^2输出1 */
#define set_P13		P13 = 1		/** 设置P1^3输出1 */
#define set_P14		P14 = 1		/** 设置P1^4输出1 */
#define set_P15		P15 = 1		/** 设置P1^5输出1 */
#define set_P16		P16 = 1		/** 设置P1^6输出1 */
#define set_P17		P17 = 1		/** 设置P1^7输出1 */

#define clr_P10		P10 = 0		/** 设置P1^0输出0 */
#define clr_P11		P11 = 0		/** 设置P1^1输出0 */
#define clr_P12		P12 = 0		/** 设置P1^2输出0 */
#define clr_P13		P13 = 0		/** 设置P1^3输出0 */
#define clr_P14		P14 = 0		/** 设置P1^4输出0 */
#define clr_P15		P15 = 0		/** 设置P1^5输出0 */
#define clr_P16		P16 = 0		/** 设置P1^6输出0 */
#define clr_P17		P17 = 0		/** 设置P1^7输出0 */

/********************************************************************************************************************************************************************************************************/

/********************************************************************************************************************************************************************************************************/
/************************* 设置P3端口输出 *************************/
#define set_P30		P30 = 1		/** 设置P3^0输出1 */
#define clr_P30		P30 = 0		/** 设置P2^0输出0 */

/********************************************************************************************************************************************************************************************************/

#endif	/** _GPIO_H_ */
