Final-Resolution/ChronoVolt/1.Hardware/ChronoVolt_Control_Rev0.3/datasheets/8-MD-06INKM模块/code/代码示例工程/test/source/user/config.h

/**
 * @file config.h
 * @author mangolu (mangolu81@gmail.com)
 * @brief 系统配置相关定义
 * @version 1.0.0
 * @date 2019-05-08
 * 
 * @copyright Copyright (c) 2019 mangolu All righits reserved
 * 
 */
#ifndef _CONFIG_H_
#define _CONFIG_H_

/** 所需头文件开始>>> */

#include "../n76e003/N76E003.h"
#include "../common/common.h"

/** 所需头文件结束<<< */

/** 需要自行定义部分开始>>> */

/************************* 系统晶振频率 *************************/
//#define FOSC 11059200UL
// #define FOSC 12000000UL
#define FOSC 16000000UL
// #define FOSC 16600000UL
//#define FOSC 22118400UL
//#define FOSC 24000000UL
//#define FOSC 33000000UL

/********************************************************************************************************************************************************************************************************/

/************************* 定时器设置 *************************/



/********************************************************************************************************************************************************************************************************/

/************************* 串口设置 *************************/


/********************************************************************************************************************************************************************************************************/

/************************* 外部中断设置 *************************/



/********************************************************************************************************************************************************************************************************/

/************************* 阻塞延迟函数开启关闭设置 *************************/


/********************************************************************************************************************************************************************************************************/

/** 需要自行定义部分结束<<< */


#endif	/** _CONFIG_H_ */
