Final-Resolution/ChronoVolt/1.Hardware/ChronoVolt_Control_Rev0.3/datasheets/8-MD-06INKM模块/code/代码示例工程/test/source/n76e003/sfr_macro.c

/**
 * @file sfr_macro.c
 * @author mangolu (mangolu81@gmail.com)
 * @brief 特殊功能寄存器操作宏定义实现
 * @version 1.0.0
 * @date 2019-05-06
 * 
 * @copyright Copyright (c) 2019 mangolu All righits reserved
 * 
 */
/** 所需头文件开始>>> */

#include "sfr_macro.h"

/** 所需头文件结束<<< */

/** 需要自行定义部分开始>>> */

/** 需要自行定义部分结束<<< */

bit BIT_TMP;	/** 比特位存储临时变量 */
