Final-Resolution/ChronoVolt/1.Hardware/ChronoVolt_Control_Rev0.3/datasheets/8-MD-06INKM模块/code/代码示例工程/test/source/n76e003/watchdog.c

/**
 * @file watchdog.c
 * @author mangolu (mangolu81@gmail.com)
 * @brief N76E003看门狗操作相关函数实现
 * @version 1.0.0
 * @date 2019-04-26
 * 
 * @copyright Copyright (c) 2019 mangolu All righits reserved
 * 
 */
#include "watchdog.h"
