Final-Resolution/ChronoVolt/1.Hardware/ChronoVolt_Control_Rev0.3/datasheets/8-MD-06INKM模块/code/代码示例工程/test/source/n76e003/watchdog.h

/**
 * @file watchdog.h
 * @author mangolu (mangolu81@gmail.com)
 * @brief N76E003看门狗操作相关函数定义
 * @version 1.0.0
 * @date 2019-04-26
 * 
 * @copyright Copyright (c) 2019 mangolu All righits reserved
 * 
 */
/********************************************************************************************************************************************************************************************************/
/************************* 看门狗(watchdog)相关寄存器 *************************/


/********************************************************************************************************************************************************************************************************/
#ifndef _WATCHDOG_H_
#define _WATCHDOG_H_

/** 所需头文件开始>>> */

// #include "N76E003.h"
// #include "common.h"
#include "watchdog.h"

/** 所需头文件结束<<< */

/** 需要自行定义部分开始>>> */



/** 需要自行定义部分结束<<< */

/********************************************************************************************************************************************************************************************************/

/*************************  *************************/


/********************************************************************************************************************************************************************************************************/


#endif	/** _WATCHDOG_H_ */
