Final-Resolution/ChronoVolt/1.Hardware/ChronoVolt_Control_Rev0.3/datasheets/8-MD-06INKM模块/code/代码示例工程/test/source/user/version.h

/**
 * @file version.h
 * @author mangolu (mangolu81@gmail.com)
 * @brief 版本号定义
 * @version 1.0.0
 * @date 2019-05-06
 * 
 * @copyright Copyright (c) 2019 mangolu All righits reserved
 * 
 */
#ifndef _VERSION_H_
#define _VERSION_H_

/** 所需头文件开始>>> */

/** 所需头文件结束<<< */

/** 需要自行定义部分开始>>> */

#define FW_Version_Major                    0x01
#define FW_Version_Minor                    0x00
#define FW_Version_Modifi                   0x00

#define Date_Y                              2019
#define Date_M                              8
#define Date_D                              9

/** 需要自行定义部分结束<<< */

#endif	/** _VERSION_H_ */
